JustSimplyKyle/rc-car/build.rs

fn main() {
    // 1. Define the path to your script
    // let script_path = "/home/kyle/coding/controller-ui/out.sh";

    // // 2. Execute the shell script
    // let status = std::process::Command::new(script_path)
    //     .status()
    //     .expect("Failed to execute out.sh");

    // // 3. Panic if the script fails (stops the build)
    // if !status.success() {
    //     panic!("out.sh failed with exit code: {:?}", status.code());
    // }

    // // 4. TRIGGER CONFIGURATION:

    // // OPTION A: Run ONLY if the script or the UI folder changes (Recommended)
    // // This tells Cargo: "If anything in the controller-ui folder changes, run this build script again."
    // println!("cargo:rerun-if-changed=/home/kyle/coding/controller-ui/src/main.rs");

    linker_be_nice();
    println!("cargo:rustc-link-arg=-Tdefmt.x");
    println!("cargo:rustc-link-arg=-Wl,--defsym=_stack_size=0x10000");
    // make sure linkall.x is the last linker script (otherwise might cause problems with flip-link)
    println!("cargo:rustc-link-arg=-Tlinkall.x");
}

fn linker_be_nice() {
    let args: Vec<String> = std::env::args().collect();
    if args.len() > 1 {
        let kind = &args[1];
        let what = &args[2];

        match kind.as_str() {
            "undefined-symbol" => match what.as_str() {
                "_defmt_timestamp" => {
                    eprintln!();
                    eprintln!("💡 `defmt` not found - make sure `defmt.x` is added as a linker script and you have included `use defmt_rtt as _;`");
                    eprintln!();
                }
                "_stack_start" => {
                    eprintln!();
                    eprintln!("💡 Is the linker script `linkall.x` missing?");
                    eprintln!();
                }
                "esp_wifi_preempt_enable"
                | "esp_wifi_preempt_yield_task"
                | "esp_wifi_preempt_task_create" => {
                    eprintln!();
                    eprintln!("💡 `esp-wifi` has no scheduler enabled. Make sure you have the `builtin-scheduler` feature enabled, or that you provide an external scheduler.");
                    eprintln!();
                }
                "embedded_test_linker_file_not_added_to_rustflags" => {
                    eprintln!();
                    eprintln!("💡 `embedded-test` not found - make sure `embedded-test.x` is added as a linker script for tests");
                    eprintln!();
                }
                _ => (),
            },
            // we don't have anything helpful for "missing-lib" yet
            _ => {
                std::process::exit(1);
            }
        }

        std::process::exit(0);
    }

    println!(
        "cargo:rustc-link-arg=-Wl,--error-handling-script={}",
        std::env::current_exe().unwrap().display()
    );
}
