JustSimplyKyle/rc-car/src/lib.rs

#![no_std]
#![feature(impl_trait_in_assoc_type)]
#![feature(type_alias_impl_trait)]
#![feature(impl_trait_in_bindings)]

pub mod ps2;

pub mod motor;
pub mod ps2_controller_task;
pub mod web;

#[macro_export]
macro_rules! mk_static {
    ($t:ty,$val:expr) => {{
        static STATIC_CELL: static_cell::StaticCell<$t> = static_cell::StaticCell::new();
        #[deny(unused_attributes)]
        let x = STATIC_CELL.uninit().write(($val));
        x
    }};
}
